smalltt/E-39_Indoor_Positioning_System/E-39 Firmware/Src/LPS/ErrorCommunicating.jpg.h

#ifndef __SoundErrorCommunicating
#define __SoundErrorCommunicating
const uint32_t ErrorCommunicating_Size = 18044;
//const uint32_t ErrorCommunicating_Size = 6;

//const uint8_t ErrorCommunicating[] = {
//65, 66, 67, 68, 69, 70
//};

const uint8_t ErrorCommunicating[] = {
255
,216
,255
,225
,10
,225
,69
,120
,105
,102
,0
,0
,77
,77
,0
,42
,0
,0
,0
,8
,0
,7
,1
,18
,0
,3
,0
,0
,0
,1
,0
,1
,0
,0
,1
,26
,0
,5
,0
,0
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
};

#endif
