smalltt/E-39_Indoor_Positioning_System/E-39 Firmware/Src/LPS/tm_stm32f4_usb_vcp.h

/**
 * @author  Tilen Majerle
 * @email   tilen@majerle.eu
 * @website http://stm32f4-discovery.com
 * @link    http://stm32f4-discovery.com/2014/08/library-24-virtual-com-port-vcp-stm32f4xx/
 * @version v1.2
 * @ide     Keil uVision
 * @license GNU GPL v3
 * @brief   USB Virtual COM Port for STM32F4xx devices
 *	
@verbatim
   ----------------------------------------------------------------------
    Copyright (C) Tilen Majerle, 2015
    
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
    You should have received a copy of the GNU General Public License
    along with this program.  If not, see <http://www.gnu.org/licenses/>.
   ----------------------------------------------------------------------
@endverbatim
 */
#ifndef TM_USB_VCP_H
#define TM_USB_VCP_H   120

/* C++ detection */
#ifdef __cplusplus
extern "C" {
#endif

/**
 * @addtogroup TM_STM32F4xx_Libraries
 * @{
 */

/**
 * @defgroup TM_USB_VCP
 * @brief    USB Virtual COM Port for STM32F4xx devices - http://stm32f4-discovery.com/2014/08/library-24-virtual-com-port-vcp-stm32f4xx/
 * @{
 *
 * With this library, your STM32F4xx will be seen to your computer as Virtual COM Port (VCP).
 * To be able to work, you have to install ST's VCP Driver, from link below:
 *
 *		http://www.st.com/web/en/catalog/tools/PF257938
 *
 * This library can work in 2 ways.
 * First and default is Full-Speed mode, second option is High-Speed mode.
 * Also, different modes have different pinouts.
 *
 * In default settings, USB FS mode is selected.
 *
 * STM32F4-Discovery has USB connected to FS mode, but
 * STM32F429-Discovery has connected it to USB HS in FS mode.
 * But if you have cable, like me, USB->4wires, you can connect Data+ and Data- to any pin on Discovery board.
 * I did this, to check, if both mdoes work on bots discovery boards and yes, it worked.
 * For security reasons set 22Ohm resistors in serial to your data pins.
 *
 * USB FS MODE (micro USB connected on STM32F4 Discovery board)
 *	- This is default option and don't need any special settings.
 *
 * \par Pinout for USB FS mode
 *
@verbatim
USB			STM32F4xx
Data +		PA12
Data -		PA11
@endverbatim
 *
 * USB HS in FS mode (micro USB connected on STM32F429 Discovery board)
 *
 *	If you are working with STM32F429 Discovery board, and you want to use microUSB connector for VCP,
 *	then set define below in your defines.h file
 *
@verbatim
//Activate USB HS in FS mode
#define USE_USB_OTG_HS
@endverbatim
 *
 * \par Pinout for USB HS in FS mode
 *
@verbatim
USB			STM32F4xx
Data +		PB15
Data -		PB14
@endverbatim
 *
 *
 * \par Changelog
 *
@verbatim
 Version 1.2
  - March 08, 2015
  - Added options to get user settings from terminal
  - Baudrate, stop bits, parity, data bits.
  - Useful if you make USB->UART converter like FTDI

 Version 1.1
  - December 27, 2014
  - Added advanced functions for string operations
  - Now, Gets function will wait till buffer is full or \n is received
  - This is prevent for while loop if \n character is not received

 Version 1.0
  - First release
@endverbatim
 *
 * \par Dependencies
 *
@verbatim
 - STM32F4xx
 - STM32F4xx RCC
 - STM32F4xx GPIO
 - STM32F4xx EXTI
 - misc.h
 - defines.h
 - USB CDC DEVICE
@endverbatim
 */

#include "stm32f4xx.h"
#include "stm32f4xx_rcc.h"
#include "stm32f4xx_gpio.h"
#include "stm32f4xx_exti.h"
#include "misc.h"
//#include "defines.h"
/* Parts of USB device */
#include "usbd_cdc_core.h"
#include "usb_conf.h"
#include "usbd_desc.h"
#include "usbd_cdc_vcp.h"

/**
 * @defgroup TM_USB_VCP_Macros
 * @brief    Library defines
 * @{
 */

/**
 * @brief  Default buffer length
 * @note   Increase this value if you need more memory for VCP receive data
 */
#ifndef USB_VCP_RECEIVE_BUFFER_LENGTH
#define USB_VCP_RECEIVE_BUFFER_LENGTH		128
#endif

/**
 * @}
 */
 
/**
 * @defgroup TM_USB_VCP_Typedefs
 * @brief    Library Typedefs
 * @{
 */

/**
 * @brief VCP Result Enumerations
 */
typedef enum {
	TM_USB_VCP_OK,                  /*!< Everything ok */
	TM_USB_VCP_ERROR,               /*!< An error occurred */
	TM_USB_VCP_RECEIVE_BUFFER_FULL, /*!< Receive buffer is full */
	TM_USB_VCP_DATA_OK,             /*!< Data OK */
	TM_USB_VCP_DATA_EMPTY,          /*!< Data empty */
	TM_USB_VCP_NOT_CONNECTED,       /*!< Not connected to PC */
	TM_USB_VCP_CONNECTED,           /*!< Connected to PC */
	TM_USB_VCP_DEVICE_SUSPENDED,    /*!< Device is suspended */
	TM_USB_VCP_DEVICE_RESUMED       /*!< Device is resumed */
} TM_USB_VCP_Result;

/**
 * @brief  Structure for USART if you are working USB/UART converter with STM32F4xx
 */
typedef struct {
	uint32_t Baudrate; /*!< Baudrate, which is set by user on terminal. 
	                        Value is number of bits per second, for example: 115200 */
	uint8_t Stopbits;  /*!< Stop bits, which is set by user on terminal.
	                        Possible values:
                               - 0: 1 stop bit
                               - 1: 1.5 stop bits
                               - 2: 2 stop bits */
	uint8_t DataBits;  /*!< Data bits, which is set by user on terminal.
                            Possible values:
                               - 5: 5 data bits
                               - 6: 6 data bits
                               - 7: 7 data bits
                               - 8: 8 data bits
                               - 9: 9 data bits */
	uint8_t Parity;    /*!< Parity, which is set by user on terminal.
                            Possible values:
                               - 0: No parity
                               - 1: Odd parity
                               - 2: Even parity
                               - 3: Mark parity
                               - 4: Space parity */
	uint8_t Changed;   /*!< When you check for settings in my function, 
	                        this will be set to 1 if user has changed parameters,
                            so you can reinitialize USART peripheral if you need to. */
} TM_USB_VCP_Settings_t;

/**
 * @}
 */

/**
 * @defgroup TM_USB_VCP_Functions
 * @brief    Library Functions
 * @{
 */
 
uint16_t TM_USB_TRANSMIT_BUFFER_COUNT();

/**
 * @brief  Initializes USB VCP
 * @param  None
 * @retval TM_USB_VCP_OK
 */
TM_USB_VCP_Result TM_USB_VCP_Init(void);

/**
 * @brief  Reads settings from user
 * @note   These settings are set in terminal on PC
 * @param  *Settings: Pointer to TM_USB_VCP_Settings_t structure where to save data
 * @retval TM_USB_VCP_OK
 */
TM_USB_VCP_Result TM_USB_VCP_GetSettings(TM_USB_VCP_Settings_t* Settings);

/**
 * @brief  Gets received character from internal buffer
 * @param  *c: pointer to store new character to
 * @retval Character status:
 *            - TM_USB_VCP_DATA_OK: Character is valid inside *c_str
 *            - TM_USB_VCP_DATA_EMPTY: No character in *c
 */
TM_USB_VCP_Result TM_USB_VCP_Getc(uint8_t* c);

/**
 * @brief  Puts character to USB VCP
 * @param  c: character to send over USB
 * @retval TM_USB_VCP_OK
 */
TM_USB_VCP_Result TM_USB_VCP_Putc(volatile char c);

/**
 * @brief  Gets string from VCP port
 *
 * @note   To use this method, you have to send \n (0x0D) at the end of your string,
 *         otherwise data can be lost and you will fall in infinite loop.
 * @param  *buffer: Pointer to buffer variable where to save string
 * @param  bufsize: Maximum buffer size
 * @retval Number of characters in buffer:
 *            - 0: String not valid
 *            - > 0: String valid, number of characters inside string
 */
uint16_t TM_USB_VCP_Gets(char* buffer, uint16_t bufsize);

/**
 * @brief  Puts string to USB VCP
 * @param  *str: Pointer to string variable
 * @retval TM_USB_VCP_OK
 */
TM_USB_VCP_Result TM_USB_VCP_Puts(char* str);

/**
 * @brief  Sends array of data to USB VCP
 * @param  *DataArray: Pointer to 8-bit data array to be sent over USB
 * @param  Length: Number of elements to sent in units of bytes
 * @retval Sending status
 */
TM_USB_VCP_Result TM_USB_VCP_Send(uint8_t* DataArray, uint32_t Length);

/**
 * @brief  Gets VCP status
 * @param  None
 * @retval Device status:
 *            - TM_USB_VCP_CONNECTED: Connected to computer
 *            - other: Not connected and not ready to communicate
 */
TM_USB_VCP_Result TM_USB_VCP_GetStatus(void);

/**
 * @brief  Checks if receive buffer is empty
 * @param  None
 * @retval Buffer status:
 *            - 0: Buffer is not empty
 *            - > 0: Buffer is empty
 */
uint8_t TM_USB_VCP_BufferEmpty(void);

/**
 * @brief  Checks if receive buffer is fukk
 * @param  None
 * @retval Buffer status:
 *            - 0: Buffer is not full
 *            - > 0: Buffer is full
 */
uint8_t TM_USB_VCP_BufferFull(void);

/**
 * @brief  Checks if character is in buffer
 * @param  c: Character to be checked if available in buffer
 * @retval Character status:
 *            - 0: Character is not in buffer
 *            - > 0: Character is in buffer
 */
uint8_t TM_USB_VCP_FindCharacter(volatile char c);

/* Internal functions */
extern TM_USB_VCP_Result TM_INT_USB_VCP_AddReceived(uint8_t c);

/**
 * @}
 */
 
/**
 * @}
 */
 
/**
 * @}
 */

/* C++ detection */
#ifdef __cplusplus
}
#endif

#endif
