smalltt/E-39_Indoor_Positioning_System/E-39 Firmware/Src/LPS/EZUtils.h

#ifndef __EZUtils
#define __EZUtils

#include <stm32f4xx_gpio.h>

bool IsBitSet(long b, int pos);

void DelayMS(uint32_t val);

void DelayUS(uint32_t val);

void DelayCycles(uint32_t val);

uint8_t Convert8(uint64_t i, uint8_t pos);

int strlen(const char s[]);

int atoi(const char s[]);

void reverse(char s[]);

#endif
